prajwal1121/Portable-Synth/Version 2 (Latest)/Software/Groovebox_Platformio/include/Mixer.h

#ifndef MIXER_H
#define MIXER_H

#include <Arduino.h>

/*
 * Output Stuff
 */
extern float outputVolume[2];

class Mixer {
  private:
    void init();
  public:
    Mixer()
    {
      init();
    }
    void menuCheck();
    void staticMenu();
};

#endif
