prajwal1121/Portable-Synth/Version 1/Code/Sequencer+Recording/1_SequenceAndRecord/9_Metronome.ino

long metronomeTimer = millis();

void metronomePlayer(){
  if (metronomeEnable == 2){
    if (millis()-metronomeTimer > ms_per_beat){
      metronome.play(AudioSampleMetronome);
      if (armLocation){
        armLocation = 0;
      }
      else{
        armLocation = 1;
      }
      metronomeTimer = millis();
    }
  }
}

void tapMetronome(){
  metronome.play(AudioSampleMetronome);
  tapTempo.update();
  bpm = tapTempo.getBPM();
}
