prajwal1121/Portable-Synth/Version 1/Code/Sequencer+Recording/1_SequenceAndRecord/AudioSampleMetronome.cpp

// Audio data converted from WAV file by wav2sketch

#include "AudioSampleMetronome.h"

// Converted from metronome.wav, using 44100 Hz, u-law encoding
const unsigned int AudioSampleMetronome[6657] = {
0x01006797,0x98800080,0x90BC182D,0x2442321B,0x94B9C3C2,0x45403931,0xC5C1B038,0x1BB8C2CC,
0x595E594E,0xE8E2CF3D,0xB4DEE4E8,0x74726859,0xC5566D73,0xEAEAE8E2,0xE0E5E9EA,0xDAC9BED1,
0x40D3E3E1,0x7E7B7361,0x6773797E,0xE3D9C151,0xF2F1EBE8,0xF8F4F1F0,0xE1F1F9FA,0x76726391,
0x787C7C79,0x75737374,0xA65A6F75,0xFEF4E6D4,0xFFFFFFFF,0xE9F4F9FC,0x675C3BD3,0x7F7F7971,
0x7C7F7F7F,0x46657278,0xF8F2E7D2,0xFFFFFFFD,0xF9FEFFFF,0x7060CCEF,0x7C7B7975,0x7F7F7F7F,
0x70797E7F,0xF8F0D558,0xFFFFFFFF,0xF6FBFEFF,0xCBE5EEF2,0x7D766B53,0x7F7F7F7F,0x6C747B7F,
0xE5D04560,0xFFFAF6F1,0xFFFFFFFF,0xD6ECF6FC,0x7672664B,0x7E7E7C79,0x7A7D7E7E,0xC15D6F76,
0xFDF9F2E6,0xFFFFFFFF,0xF0F6FAFD,0x6A56C5E4,0x7F7D7973,0x7D7F7F7F,0x5E6D757A,0xF7F0E1A5,
0xFFFFFFFD,0xF7FCFEFF,0x4FCCE4F0,0x7D787266,0x7E7F7F7F,0x6A747A7C,0xEBDDAC58,0xFFFDF9F4,
0xFBFDFEFF,0xC5E4F1F7,0x76726753,0x7D7D7C7A,0x72767A7C,0xD73B606B,0xFBF7F3EA,0xFAFDFDFD,
0xE0EBF3F7,0x6C6147C7,0x7B797672,0x75787B7C,0xB3536570,0xF4F0E7DA,0xF9F9F9F7,0xEAF1F5F7,
0x624CC2DF,0x7775726C,0x74767778,0x52626B71,0xEDE4D6A2,0xF6F6F4F2,0xEDF2F4F6,0x4BB2D7E5,
0x726E675E,0x73747474,0x5E676E72,0xE2D3A94B,0xF3F2EFE9,0xEEF1F2F3,0xA9D3E1E8,0x6A655C4B,
0x7171706F,0x63696E70,0xD6BF4057,0xEEEBE7E1,0xEBEEEFEF,0xCFDBE3E8,0x635A49A2,0x6E6D6B67,
0x62666A6D,0xC032505A,0xE6E3DDD3,0xE9EAEAE9,0xD1DCE3E7,0x595036B9,0x66656360,0x61646666,
0x0246545C,0xE1DCD4C5,0xE3E4E4E3,0xD3D9DFE1,0x4B34B0C8,0x62605C55,0x5F616263,0x24435159,
0xD6D0C5B3,0xE0E0DFDB,0xD3D9DDE0,0x452BB5C8,0x5E5C5851,0x55595B5D,0x273E4850,0xCCC5BDA7,
0xD8D7D4D1,0xC9D1D5D8,0x413394BC,0x4D4B4946,0x4D50504E,0x3441464A,0xC3BDB010,0xCCCBC9C6,
0xBABFC4C9,0x3011A2B3,0x44403B38,0x3A404344,0x9E122E36,0xB8B3ABA4,0xBEC0C1BE,0x21A4B7BF,
0x41403C35,0x3032373E,0x182A2C2B,0xB1A19189,0xC6C8C5BF,0x9CB4C0C4,0x403E3623,0x41404040,
0x41434442,0xAC20343C,0xCCCAC7C1,0xC3C8CACC,0xAFB5B8BD,0x403315A3,0x52524F48,0x3B444D51,
0xB1A30D30,0xC7C2BDB8,0xD1D1CFCB,0xB2C3CBD0,0x46423922,0x4B4C4B4A,0x48494949,0x0D374246,
0xCDC7C0B2,0xCCD1D2D1,0xBAC0C2C6,0x302499B2,0x504A4338,0x494D5151,0x03313F45,0xC0BAB8B0,
0xC9C8C6C4,0xC2C6C8C9,0x169AAFB9,0x4540362A,0x47474747,0x36404446,0xB9AC0D2B,0xC3C1C0BF,
0xC5C6C6C5,0xA6B9C2C5,0x4540351F,0x484A4948,0x29323D44,0xA3012026,0xC4C0BBB2,0xC8C9C8C6,
0x1C9BB5C2,0x3E3A332A,0x3633373C,0x4041403D,0x182D353B,0xC4C2B8A4,0xC1C3C5C5,0x99A6B2BC,
0x28201505,0x3D3C3A33,0x4141403E,0x9120303A,0xC0BBB4A8,0xC2C3C3C1,0xA2AEB6BD,0x35281292,
0x4644423E,0x2F3A4246,0xBBB2A213,0xBABEC0C0,0xA0A7B1B6,0xAAA8A19B,0x372E159E,0x393D3C3A,
0xA3892332,0x8FA1A9A9,0x94870C0F,0xB2B1ACA2,0x27179BAC,0x282D2D2B,0xA095011D,0x9198A0A1,
0xA6A2978F,0xADAFACA9,0x2B208AA3,0x3534312F,0x23252C32,0x81182425,0xB3ADA397,0xBDBCBAB7,
0xA4AFB6BB,0x31271491,0x413E3935,0x343C4142,0x841D282F,0xB9B4B0A2,0xC3C2C1BE,0xB6BDC0C2,
0x2E2093AB,0x403E3B36,0x44424140,0x333C4345,0xBEB29C21,0xC4C6C6C4,0xBEC1C2C2,0xA4AFB4B9,
0x42392A00,0x4C4C4A46,0x333F4549,0xA89E8522,0xC4C1BAB3,0xCBCCCBC8,0xB2BCC3C8,0x3F372798,
0x48464342,0x484A4A49,0x26374044,0xC8C2B69C,0xCCCCCBCA,0xC0C4C7CA,0x298BAEB9,0x49444037,
0x4A4C4D4C,0x34404447,0xB9AD9422,0xCBCAC6C2,0xC6C9CBCC,0x9AB1BCC2,0x423C3423,0x4C4C4A46,
0x3F44484A,0xA8912033,0xC6C3BFB5,0xCCCCCAC8,0xB3BDC3C8,0x3E35239B,0x48474543,0x46474849,
0x28374044,0xC5C0B599,0xCACBCAC8,0xBEC3C7C9,0x2790ACB6,0x48444036,0x494B4C4B,0x2F3A4246,
0xB9B09F16,0xC9C8C5C1,0xC3C6C8C9,0x82A9B5BE,0x433C3327,0x49494745,0x38414547,0xB3A5072A,
0xC2C3C1BC,0xC6C5C3C2,0xB1B8C0C4,0x4239249F,0x44454645,0x38404243,0x99062430,0xBFB6ADA2,
0xC5C5C5C3,0xAEB9C0C3,0x29231695,0x43413B32,0x42444444,0x23323A40,0xB8B3A98A,0xC3C4C2BE,
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
};
