prajwal1121/Portable-Synth/Version 1/Code/Sequencer+Recording/1_SequenceAndRecord/Ocarina_samples.cpp

#include "Ocarina_samples.h"
const AudioSynthWavetable::sample_data Ocarina_samples[3] = {
	{
		(int16_t*)sample_0_Ocarina_OcarinaF4,	//16-bit PCM encoded audio sample
		true,	//Whether or not to loop this sample
		12,	//Number of bits needed to hold length
		(1048576*1.0227829387472833*(44100.0 / AUDIO_SAMPLE_RATE_EXACT)) / 1318.5102276514797 + 0.5,	//((0x80000000 >> (index_bits - 1)) * cents_offset * sampling_rate / AUDIO_SAME_RATE_EXACT) / sample_freq + 0.5
		((uint32_t)2847-1) << (32 - 12),	//(sample_length-1) << (32 - sample_length_bits)
		((uint32_t)2839-1) << (32 - 12),	//(loop_end-1) << (32 - sample_length_bits) == LOOP_PHASE_END
		(((uint32_t)2839-1) << (32 - 12)) - (((uint32_t)1438-1) << (32 - 12)),	//LOOP_PHASE_END - (loop_start-1) << (32 - sample_length_bits) == LOOP_PHASE_END - LOOP_PHASE_START == LOOP_PHASE_LENGTH
		uint16_t(UINT16_MAX * WAVETABLE_DECIBEL_SHIFT(-170/100.0)), //INITIAL_ATTENUATION_SCALAR
		uint32_t(0*AudioSynthWavetable::SAMPLES_PER_MSEC/8.0+0.5),	//DELAY_COUNT
		uint32_t(7*AudioSynthWavetable::SAMPLES_PER_MSEC/8.0+0.5),	//ATTACK_COUNT
		uint32_t(0*AudioSynthWavetable::SAMPLES_PER_MSEC/8.0+0.5),	//HOLD_COUNT
		uint32_t(1730*AudioSynthWavetable::SAMPLES_PER_MSEC/8.0+0.5),	//DECAY_COUNT
		uint32_t(321*AudioSynthWavetable::SAMPLES_PER_MSEC/8.0+0.5),	//RELEASE_COUNT
		int32_t(0*AudioSynthWavetable::UNITY_GAIN),	//SUSTAIN_MULT
		uint32_t(9 * AudioSynthWavetable::SAMPLES_PER_MSEC / (2 * AudioSynthWavetable::LFO_PERIOD)), 	// VIBRATO_DELAY
		uint32_t(4288/1000.0 * AudioSynthWavetable::LFO_PERIOD * (UINT32_MAX / AUDIO_SAMPLE_RATE_EXACT)), // VIBRATO_INCREMENT
		(WAVETABLE_CENTS_SHIFT(-0/1000.0) - 1.0)*4, // VIBRATO_PITCH_COEFFICIENT_INITIAL
		(1.0 - WAVETABLE_CENTS_SHIFT(0/1000.0))*4, // VIBRATO_COEFFICIENT_SECONDARY
		uint32_t(14 * AudioSynthWavetable::SAMPLES_PER_MSEC / (2 * AudioSynthWavetable::LFO_PERIOD)), // MODULATION_DELAY
		uint32_t(4288/1000.0 * AudioSynthWavetable::LFO_PERIOD * (UINT32_MAX / AUDIO_SAMPLE_RATE_EXACT)), // MODULATION_INCREMENT
		(WAVETABLE_CENTS_SHIFT(-0/1000.0) - 1.0)*4, // MODULATION_PITCH_COEFFICIENT_INITIAL
		(1.0 - WAVETABLE_CENTS_SHIFT(0/1000.0))*4, // MODULATION_PITCH_COEFFICIENT_SECOND
		int32_t(UINT16_MAX * (WAVETABLE_DECIBEL_SHIFT(-0.1) - 1.0)) *4, // MODULATION_AMPLITUDE_INITIAL_GAIN
		int32_t(UINT16_MAX * (1.0 - WAVETABLE_DECIBEL_SHIFT(0.1))) *4, // MODULATION_AMPLITUDE_FINAL_GAIN
	},
	{
		(int16_t*)sample_1_Ocarina_OcarinaF4,	//16-bit PCM encoded audio sample
		true,	//Whether or not to loop this sample
		12,	//Number of bits needed to hold length
		(1048576*1.023373891996775*(44100.0 / AUDIO_SAMPLE_RATE_EXACT)) / 1318.5102276514797 + 0.5,	//((0x80000000 >> (index_bits - 1)) * cents_offset * sampling_rate / AUDIO_SAME_RATE_EXACT) / sample_freq + 0.5
		((uint32_t)2847-1) << (32 - 12),	//(sample_length-1) << (32 - sample_length_bits)
		((uint32_t)2839-1) << (32 - 12),	//(loop_end-1) << (32 - sample_length_bits) == LOOP_PHASE_END
		(((uint32_t)2839-1) << (32 - 12)) - (((uint32_t)1438-1) << (32 - 12)),	//LOOP_PHASE_END - (loop_start-1) << (32 - sample_length_bits) == LOOP_PHASE_END - LOOP_PHASE_START == LOOP_PHASE_LENGTH
		uint16_t(UINT16_MAX * WAVETABLE_DECIBEL_SHIFT(-100/100.0)), //INITIAL_ATTENUATION_SCALAR
		uint32_t(0*AudioSynthWavetable::SAMPLES_PER_MSEC/8.0+0.5),	//DELAY_COUNT
		uint32_t(7*AudioSynthWavetable::SAMPLES_PER_MSEC/8.0+0.5),	//ATTACK_COUNT
		uint32_t(0*AudioSynthWavetable::SAMPLES_PER_MSEC/8.0+0.5),	//HOLD_COUNT
		uint32_t(1730*AudioSynthWavetable::SAMPLES_PER_MSEC/8.0+0.5),	//DECAY_COUNT
		uint32_t(321*AudioSynthWavetable::SAMPLES_PER_MSEC/8.0+0.5),	//RELEASE_COUNT
		int32_t(0*AudioSynthWavetable::UNITY_GAIN),	//SUSTAIN_MULT
		uint32_t(9 * AudioSynthWavetable::SAMPLES_PER_MSEC / (2 * AudioSynthWavetable::LFO_PERIOD)), 	// VIBRATO_DELAY
		uint32_t(4288/1000.0 * AudioSynthWavetable::LFO_PERIOD * (UINT32_MAX / AUDIO_SAMPLE_RATE_EXACT)), // VIBRATO_INCREMENT
		(WAVETABLE_CENTS_SHIFT(-0/1000.0) - 1.0)*4, // VIBRATO_PITCH_COEFFICIENT_INITIAL
		(1.0 - WAVETABLE_CENTS_SHIFT(0/1000.0))*4, // VIBRATO_COEFFICIENT_SECONDARY
		uint32_t(14 * AudioSynthWavetable::SAMPLES_PER_MSEC / (2 * AudioSynthWavetable::LFO_PERIOD)), // MODULATION_DELAY
		uint32_t(4288/1000.0 * AudioSynthWavetable::LFO_PERIOD * (UINT32_MAX / AUDIO_SAMPLE_RATE_EXACT)), // MODULATION_INCREMENT
		(WAVETABLE_CENTS_SHIFT(-0/1000.0) - 1.0)*4, // MODULATION_PITCH_COEFFICIENT_INITIAL
		(1.0 - WAVETABLE_CENTS_SHIFT(0/1000.0))*4, // MODULATION_PITCH_COEFFICIENT_SECOND
		int32_t(UINT16_MAX * (WAVETABLE_DECIBEL_SHIFT(-0.1) - 1.0)) *4, // MODULATION_AMPLITUDE_INITIAL_GAIN
		int32_t(UINT16_MAX * (1.0 - WAVETABLE_DECIBEL_SHIFT(0.1))) *4, // MODULATION_AMPLITUDE_FINAL_GAIN
	},
	{
		(int16_t*)sample_2_Ocarina_OcarinaF6,	//16-bit PCM encoded audio sample
		true,	//Whether or not to loop this sample
		9,	//Number of bits needed to hold length
		(8388608*1.0*(44100.0 / AUDIO_SAMPLE_RATE_EXACT)) / 4434.922095629953 + 0.5,	//((0x80000000 >> (index_bits - 1)) * cents_offset * sampling_rate / AUDIO_SAME_RATE_EXACT) / sample_freq + 0.5
		((uint32_t)349-1) << (32 - 9),	//(sample_length-1) << (32 - sample_length_bits)
		((uint32_t)341-1) << (32 - 9),	//(loop_end-1) << (32 - sample_length_bits) == LOOP_PHASE_END
		(((uint32_t)341-1) << (32 - 9)) - (((uint32_t)331-1) << (32 - 9)),	//LOOP_PHASE_END - (loop_start-1) << (32 - sample_length_bits) == LOOP_PHASE_END - LOOP_PHASE_START == LOOP_PHASE_LENGTH
		uint16_t(UINT16_MAX * WAVETABLE_DECIBEL_SHIFT(-170/100.0)), //INITIAL_ATTENUATION_SCALAR
		uint32_t(0*AudioSynthWavetable::SAMPLES_PER_MSEC/8.0+0.5),	//DELAY_COUNT
		uint32_t(10*AudioSynthWavetable::SAMPLES_PER_MSEC/8.0+0.5),	//ATTACK_COUNT
		uint32_t(0*AudioSynthWavetable::SAMPLES_PER_MSEC/8.0+0.5),	//HOLD_COUNT
		uint32_t(1730*AudioSynthWavetable::SAMPLES_PER_MSEC/8.0+0.5),	//DECAY_COUNT
		uint32_t(321*AudioSynthWavetable::SAMPLES_PER_MSEC/8.0+0.5),	//RELEASE_COUNT
		int32_t(0*AudioSynthWavetable::UNITY_GAIN),	//SUSTAIN_MULT
		uint32_t(9 * AudioSynthWavetable::SAMPLES_PER_MSEC / (2 * AudioSynthWavetable::LFO_PERIOD)), 	// VIBRATO_DELAY
		uint32_t(4288/1000.0 * AudioSynthWavetable::LFO_PERIOD * (UINT32_MAX / AUDIO_SAMPLE_RATE_EXACT)), // VIBRATO_INCREMENT
		(WAVETABLE_CENTS_SHIFT(-0/1000.0) - 1.0)*4, // VIBRATO_PITCH_COEFFICIENT_INITIAL
		(1.0 - WAVETABLE_CENTS_SHIFT(0/1000.0))*4, // VIBRATO_COEFFICIENT_SECONDARY
		uint32_t(14 * AudioSynthWavetable::SAMPLES_PER_MSEC / (2 * AudioSynthWavetable::LFO_PERIOD)), // MODULATION_DELAY
		uint32_t(4288/1000.0 * AudioSynthWavetable::LFO_PERIOD * (UINT32_MAX / AUDIO_SAMPLE_RATE_EXACT)), // MODULATION_INCREMENT
		(WAVETABLE_CENTS_SHIFT(-0/1000.0) - 1.0)*4, // MODULATION_PITCH_COEFFICIENT_INITIAL
		(1.0 - WAVETABLE_CENTS_SHIFT(0/1000.0))*4, // MODULATION_PITCH_COEFFICIENT_SECOND
		int32_t(UINT16_MAX * (WAVETABLE_DECIBEL_SHIFT(-0.1) - 1.0)) *4, // MODULATION_AMPLITUDE_INITIAL_GAIN
		int32_t(UINT16_MAX * (1.0 - WAVETABLE_DECIBEL_SHIFT(0.1))) *4, // MODULATION_AMPLITUDE_FINAL_GAIN
	},
};

PROGMEM const uint32_t sample_0_Ocarina_OcarinaF4[1536] = {
0x016601b0,0x01550152,0x0180014c,0x019a01b7,0x025c01d8,0x030a02b4,0x026c02e9,0x01900220,
0x012300de,0x00db0106,0x01a7016e,0x0089011f,0x005a0012,0x005a0051,0x01ac00e3,0x01b60199,
0x00cd0155,0x016d0152,0x01e901c8,0x012f01aa,0x014a0190,0x01b00166,0x025e028b,0x02920268,
0x018b021a,0x012d00f6,0x01ac01b7,0x028e01f1,0x029502f2,0x01d201fb,0x01590215,0x00fa011a,
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
0x00000000,0x00000000,0x00000000,0x00000000,0x00000000,0x00000000,0x00000000,0x00000000,
0x00000000,0x00000000,0x00000000,0x00000000,0x00000000,0x00000000,0x00000000,0x00000000,
0x00000000,0x00000000,0x00000000,0x00000000,
};
