prajwal1121/Portable-Synth/Version 1/Code/Sequencer+Recording/1_SequenceAndRecord/Pizzicato_samples.cpp

#include "Pizzicato_samples.h"
const AudioSynthWavetable::sample_data Pizzicato_samples[4] = {
	{
		(int16_t*)sample_0_Pizzicato_PizzViolinE3,	//16-bit PCM encoded audio sample
		true,	//Whether or not to loop this sample
		13,	//Number of bits needed to hold length
		(524288*1.0*(44100.0 / AUDIO_SAMPLE_RATE_EXACT)) / 622.2539674441618 + 0.5,	//((0x80000000 >> (index_bits - 1)) * cents_offset * sampling_rate / AUDIO_SAME_RATE_EXACT) / sample_freq + 0.5
		((uint32_t)5687-1) << (32 - 13),	//(sample_length-1) << (32 - sample_length_bits)
		((uint32_t)5679-1) << (32 - 13),	//(loop_end-1) << (32 - sample_length_bits) == LOOP_PHASE_END
		(((uint32_t)5679-1) << (32 - 13)) - (((uint32_t)5608-1) << (32 - 13)),	//LOOP_PHASE_END - (loop_start-1) << (32 - sample_length_bits) == LOOP_PHASE_END - LOOP_PHASE_START == LOOP_PHASE_LENGTH
		uint16_t(UINT16_MAX * WAVETABLE_DECIBEL_SHIFT(-550/100.0)), //INITIAL_ATTENUATION_SCALAR
		uint32_t(0*AudioSynthWavetable::SAMPLES_PER_MSEC/8.0+0.5),	//DELAY_COUNT
		uint32_t(0*AudioSynthWavetable::SAMPLES_PER_MSEC/8.0+0.5),	//ATTACK_COUNT
		uint32_t(0*AudioSynthWavetable::SAMPLES_PER_MSEC/8.0+0.5),	//HOLD_COUNT
		uint32_t(4110*AudioSynthWavetable::SAMPLES_PER_MSEC/8.0+0.5),	//DECAY_COUNT
		uint32_t(2940*AudioSynthWavetable::SAMPLES_PER_MSEC/8.0+0.5),	//RELEASE_COUNT
		int32_t(1*AudioSynthWavetable::UNITY_GAIN),	//SUSTAIN_MULT
		uint32_t(9 * AudioSynthWavetable::SAMPLES_PER_MSEC / (2 * AudioSynthWavetable::LFO_PERIOD)), 	// VIBRATO_DELAY
		uint32_t(5129/1000.0 * AudioSynthWavetable::LFO_PERIOD * (UINT32_MAX / AUDIO_SAMPLE_RATE_EXACT)), // VIBRATO_INCREMENT
		(WAVETABLE_CENTS_SHIFT(-0/1000.0) - 1.0)*4, // VIBRATO_PITCH_COEFFICIENT_INITIAL
		(1.0 - WAVETABLE_CENTS_SHIFT(0/1000.0))*4, // VIBRATO_COEFFICIENT_SECONDARY
		uint32_t(9 * AudioSynthWavetable::SAMPLES_PER_MSEC / (2 * AudioSynthWavetable::LFO_PERIOD)), // MODULATION_DELAY
		uint32_t(5129/1000.0 * AudioSynthWavetable::LFO_PERIOD * (UINT32_MAX / AUDIO_SAMPLE_RATE_EXACT)), // MODULATION_INCREMENT
		(WAVETABLE_CENTS_SHIFT(-0/1000.0) - 1.0)*4, // MODULATION_PITCH_COEFFICIENT_INITIAL
		(1.0 - WAVETABLE_CENTS_SHIFT(0/1000.0))*4, // MODULATION_PITCH_COEFFICIENT_SECOND
		int32_t(UINT16_MAX * (WAVETABLE_DECIBEL_SHIFT(-0.1) - 1.0)) *4, // MODULATION_AMPLITUDE_INITIAL_GAIN
		int32_t(UINT16_MAX * (1.0 - WAVETABLE_DECIBEL_SHIFT(0.1))) *4, // MODULATION_AMPLITUDE_FINAL_GAIN
	},
	{
		(int16_t*)sample_1_Pizzicato_PizzViolinC4,	//16-bit PCM encoded audio sample
		true,	//Whether or not to loop this sample
		13,	//Number of bits needed to hold length
		(524288*1.0*(44100.0 / AUDIO_SAMPLE_RATE_EXACT)) / 1046.5022612023945 + 0.5,	//((0x80000000 >> (index_bits - 1)) * cents_offset * sampling_rate / AUDIO_SAME_RATE_EXACT) / sample_freq + 0.5
		((uint32_t)4607-1) << (32 - 13),	//(sample_length-1) << (32 - sample_length_bits)
		((uint32_t)4599-1) << (32 - 13),	//(loop_end-1) << (32 - sample_length_bits) == LOOP_PHASE_END
		(((uint32_t)4599-1) << (32 - 13)) - (((uint32_t)4557-1) << (32 - 13)),	//LOOP_PHASE_END - (loop_start-1) << (32 - sample_length_bits) == LOOP_PHASE_END - LOOP_PHASE_START == LOOP_PHASE_LENGTH
		uint16_t(UINT16_MAX * WAVETABLE_DECIBEL_SHIFT(-550/100.0)), //INITIAL_ATTENUATION_SCALAR
		uint32_t(0*AudioSynthWavetable::SAMPLES_PER_MSEC/8.0+0.5),	//DELAY_COUNT
		uint32_t(0*AudioSynthWavetable::SAMPLES_PER_MSEC/8.0+0.5),	//ATTACK_COUNT
		uint32_t(0*AudioSynthWavetable::SAMPLES_PER_MSEC/8.0+0.5),	//HOLD_COUNT
		uint32_t(3929*AudioSynthWavetable::SAMPLES_PER_MSEC/8.0+0.5),	//DECAY_COUNT
		uint32_t(2849*AudioSynthWavetable::SAMPLES_PER_MSEC/8.0+0.5),	//RELEASE_COUNT
		int32_t(1*AudioSynthWavetable::UNITY_GAIN),	//SUSTAIN_MULT
		uint32_t(9 * AudioSynthWavetable::SAMPLES_PER_MSEC / (2 * AudioSynthWavetable::LFO_PERIOD)), 	// VIBRATO_DELAY
		uint32_t(5129/1000.0 * AudioSynthWavetable::LFO_PERIOD * (UINT32_MAX / AUDIO_SAMPLE_RATE_EXACT)), // VIBRATO_INCREMENT
		(WAVETABLE_CENTS_SHIFT(-0/1000.0) - 1.0)*4, // VIBRATO_PITCH_COEFFICIENT_INITIAL
		(1.0 - WAVETABLE_CENTS_SHIFT(0/1000.0))*4, // VIBRATO_COEFFICIENT_SECONDARY
		uint32_t(9 * AudioSynthWavetable::SAMPLES_PER_MSEC / (2 * AudioSynthWavetable::LFO_PERIOD)), // MODULATION_DELAY
		uint32_t(5129/1000.0 * AudioSynthWavetable::LFO_PERIOD * (UINT32_MAX / AUDIO_SAMPLE_RATE_EXACT)), // MODULATION_INCREMENT
		(WAVETABLE_CENTS_SHIFT(-0/1000.0) - 1.0)*4, // MODULATION_PITCH_COEFFICIENT_INITIAL
		(1.0 - WAVETABLE_CENTS_SHIFT(0/1000.0))*4, // MODULATION_PITCH_COEFFICIENT_SECOND
		int32_t(UINT16_MAX * (WAVETABLE_DECIBEL_SHIFT(-0.1) - 1.0)) *4, // MODULATION_AMPLITUDE_INITIAL_GAIN
		int32_t(UINT16_MAX * (1.0 - WAVETABLE_DECIBEL_SHIFT(0.1))) *4, // MODULATION_AMPLITUDE_FINAL_GAIN
	},
	{
		(int16_t*)sample_2_Pizzicato_PizzViolinE5,	//16-bit PCM encoded audio sample
		true,	//Whether or not to loop this sample
		11,	//Number of bits needed to hold length
		(2097152*1.0157180609309646*(44100.0 / AUDIO_SAMPLE_RATE_EXACT)) / 2793.825851464031 + 0.5,	//((0x80000000 >> (index_bits - 1)) * cents_offset * sampling_rate / AUDIO_SAME_RATE_EXACT) / sample_freq + 0.5
		((uint32_t)1355-1) << (32 - 11),	//(sample_length-1) << (32 - sample_length_bits)
		((uint32_t)1347-1) << (32 - 11),	//(loop_end-1) << (32 - sample_length_bits) == LOOP_PHASE_END
		(((uint32_t)1347-1) << (32 - 11)) - (((uint32_t)1331-1) << (32 - 11)),	//LOOP_PHASE_END - (loop_start-1) << (32 - sample_length_bits) == LOOP_PHASE_END - LOOP_PHASE_START == LOOP_PHASE_LENGTH
		uint16_t(UINT16_MAX * WAVETABLE_DECIBEL_SHIFT(-550/100.0)), //INITIAL_ATTENUATION_SCALAR
		uint32_t(0*AudioSynthWavetable::SAMPLES_PER_MSEC/8.0+0.5),	//DELAY_COUNT
		uint32_t(0*AudioSynthWavetable::SAMPLES_PER_MSEC/8.0+0.5),	//ATTACK_COUNT
		uint32_t(0*AudioSynthWavetable::SAMPLES_PER_MSEC/8.0+0.5),	//HOLD_COUNT
		uint32_t(2569*AudioSynthWavetable::SAMPLES_PER_MSEC/8.0+0.5),	//DECAY_COUNT
		uint32_t(1449*AudioSynthWavetable::SAMPLES_PER_MSEC/8.0+0.5),	//RELEASE_COUNT
		int32_t(1*AudioSynthWavetable::UNITY_GAIN),	//SUSTAIN_MULT
		uint32_t(9 * AudioSynthWavetable::SAMPLES_PER_MSEC / (2 * AudioSynthWavetable::LFO_PERIOD)), 	// VIBRATO_DELAY
		uint32_t(5129/1000.0 * AudioSynthWavetable::LFO_PERIOD * (UINT32_MAX / AUDIO_SAMPLE_RATE_EXACT)), // VIBRATO_INCREMENT
		(WAVETABLE_CENTS_SHIFT(-0/1000.0) - 1.0)*4, // VIBRATO_PITCH_COEFFICIENT_INITIAL
		(1.0 - WAVETABLE_CENTS_SHIFT(0/1000.0))*4, // VIBRATO_COEFFICIENT_SECONDARY
		uint32_t(9 * AudioSynthWavetable::SAMPLES_PER_MSEC / (2 * AudioSynthWavetable::LFO_PERIOD)), // MODULATION_DELAY
		uint32_t(5129/1000.0 * AudioSynthWavetable::LFO_PERIOD * (UINT32_MAX / AUDIO_SAMPLE_RATE_EXACT)), // MODULATION_INCREMENT
		(WAVETABLE_CENTS_SHIFT(-0/1000.0) - 1.0)*4, // MODULATION_PITCH_COEFFICIENT_INITIAL
		(1.0 - WAVETABLE_CENTS_SHIFT(0/1000.0))*4, // MODULATION_PITCH_COEFFICIENT_SECOND
		int32_t(UINT16_MAX * (WAVETABLE_DECIBEL_SHIFT(-0.1) - 1.0)) *4, // MODULATION_AMPLITUDE_INITIAL_GAIN
		int32_t(UINT16_MAX * (1.0 - WAVETABLE_DECIBEL_SHIFT(0.1))) *4, // MODULATION_AMPLITUDE_FINAL_GAIN
	},
	{
		(int16_t*)sample_3_Pizzicato_PizzViolinE5,	//16-bit PCM encoded audio sample
		true,	//Whether or not to loop this sample
		11,	//Number of bits needed to hold length
		(2097152*1.0157180609309646*(44100.0 / AUDIO_SAMPLE_RATE_EXACT)) / 2793.825851464031 + 0.5,	//((0x80000000 >> (index_bits - 1)) * cents_offset * sampling_rate / AUDIO_SAME_RATE_EXACT) / sample_freq + 0.5
		((uint32_t)1355-1) << (32 - 11),	//(sample_length-1) << (32 - sample_length_bits)
		((uint32_t)1347-1) << (32 - 11),	//(loop_end-1) << (32 - sample_length_bits) == LOOP_PHASE_END
		(((uint32_t)1347-1) << (32 - 11)) - (((uint32_t)1331-1) << (32 - 11)),	//LOOP_PHASE_END - (loop_start-1) << (32 - sample_length_bits) == LOOP_PHASE_END - LOOP_PHASE_START == LOOP_PHASE_LENGTH
		uint16_t(UINT16_MAX * WAVETABLE_DECIBEL_SHIFT(-550/100.0)), //INITIAL_ATTENUATION_SCALAR
		uint32_t(0*AudioSynthWavetable::SAMPLES_PER_MSEC/8.0+0.5),	//DELAY_COUNT
		uint32_t(0*AudioSynthWavetable::SAMPLES_PER_MSEC/8.0+0.5),	//ATTACK_COUNT
		uint32_t(0*AudioSynthWavetable::SAMPLES_PER_MSEC/8.0+0.5),	//HOLD_COUNT
		uint32_t(2329*AudioSynthWavetable::SAMPLES_PER_MSEC/8.0+0.5),	//DECAY_COUNT
		uint32_t(1309*AudioSynthWavetable::SAMPLES_PER_MSEC/8.0+0.5),	//RELEASE_COUNT
		int32_t(1*AudioSynthWavetable::UNITY_GAIN),	//SUSTAIN_MULT
		uint32_t(9 * AudioSynthWavetable::SAMPLES_PER_MSEC / (2 * AudioSynthWavetable::LFO_PERIOD)), 	// VIBRATO_DELAY
		uint32_t(5129/1000.0 * AudioSynthWavetable::LFO_PERIOD * (UINT32_MAX / AUDIO_SAMPLE_RATE_EXACT)), // VIBRATO_INCREMENT
		(WAVETABLE_CENTS_SHIFT(-0/1000.0) - 1.0)*4, // VIBRATO_PITCH_COEFFICIENT_INITIAL
		(1.0 - WAVETABLE_CENTS_SHIFT(0/1000.0))*4, // VIBRATO_COEFFICIENT_SECONDARY
		uint32_t(9 * AudioSynthWavetable::SAMPLES_PER_MSEC / (2 * AudioSynthWavetable::LFO_PERIOD)), // MODULATION_DELAY
		uint32_t(5129/1000.0 * AudioSynthWavetable::LFO_PERIOD * (UINT32_MAX / AUDIO_SAMPLE_RATE_EXACT)), // MODULATION_INCREMENT
		(WAVETABLE_CENTS_SHIFT(-0/1000.0) - 1.0)*4, // MODULATION_PITCH_COEFFICIENT_INITIAL
		(1.0 - WAVETABLE_CENTS_SHIFT(0/1000.0))*4, // MODULATION_PITCH_COEFFICIENT_SECOND
		int32_t(UINT16_MAX * (WAVETABLE_DECIBEL_SHIFT(-0.1) - 1.0)) *4, // MODULATION_AMPLITUDE_INITIAL_GAIN
		int32_t(UINT16_MAX * (1.0 - WAVETABLE_DECIBEL_SHIFT(0.1))) *4, // MODULATION_AMPLITUDE_FINAL_GAIN
	},
};

PROGMEM const uint32_t sample_0_Pizzicato_PizzViolinE3[2944] = {
0xffeeffbc,0x03230104,0x062004f3,0x0d4f07cb,0x1c351736,0x16ae18bd,0x1cad1a19,0x1ed81ede,
0x1a1b1b79,0x1ea61c1e,0x11081a2f,0x074a0a00,0x034305c7,0x012e02b7,0xf781fc58,0xf5d7f770,
0xeee8f0ff,0xf371f15c,0xef28f0cc,0xede5f0bd,0xe732e7dd,0xebbbea4d,0xed82eb55,0xf290f040,
0xee91f29a,0xf701f0c4,0xf7a6f4b1,0xfdd4fe96,0xf0b0f71e,0xfbbef36a,0x092e02ae,0x0ced0f60,
0x0d2608b1,0x0458132a,0x0e8806b3,0x1a481173,0x20e522d4,0x27291a4f,0x08911e87,0x09ee04e7,
0x1da30f8e,0x2bd62b41,0x0c131ff1,0xe059ed1c,0xf1fbe235,0xf8c8f96b,0xd543ee0c,0xd6ead00b,
0xd392d175,0xee0ae952,0xe826e46f,0xdcd5e6c6,0xe04ee179,0xe420e191,0x06edf0d0,0x0cf50986,
0xf7dd0c93,0x080ff61d,0x05440d94,0x0cc702b9,0x1e411675,0x2129212d,0x1e9e22df,0xfecc0f69,
0x061afdcd,0x219c14d3,0x1e6a247a,0x07fa1447,0xfc4ffe52,0x122d04fd,0x2f712104,0x27a43038,
0x3545292a,0x2fc73706,0x1b0626f1,0x116c118a,0x190a1217,0x02cf1843,0xde2aed6f,0xd609d122,
0xe451e85f,0xa074c17b,0x9ad39b63,0xb5149f6a,0xb084ba89,0xb02dae2b,0xb9fab61d,0xab0eb1f3,
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
0xecf1f10a,0x1787f8db,0x1d112e11,0x1bea2928,0xd656f0c7,0xe3b3c384,0x03e8f3b7,0x146615cd,
0x01230976,0x28150a4b,0x12462dce,0xfc8413a9,0xc093dd15,0xda66b3a6,0x0630f258,0x1149124b,
0x00270dbe,0x358f0ed6,0x1c22324c,0x02d81c21,0xc564ed27,0xe4abc1c7,0x13c5fd95,0x101b152a,
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
};
