prajwal1121/Portable-Synth/Version 1/Code/Sequencer+Recording/1_SequenceAndRecord/distortiongt_samples.cpp

#include "distortiongt_samples.h"
const AudioSynthWavetable::sample_data distortiongt_samples[4] = {
	{
		(int16_t*)sample_0_distortiongt_distgtra2, // sample
		true, // LOOP
		11, // LENGTH_BITS
		(1 << (32 - 11)) * WAVETABLE_CENTS_SHIFT(-45) * 44100.0 / WAVETABLE_NOTE_TO_FREQUENCY(72) / AUDIO_SAMPLE_RATE_EXACT + 0.5, // PER_HERTZ_PHASE_INCREMENT
		((uint32_t)1831 - 1) << (32 - 11), // MAX_PHASE
		((uint32_t)1827 - 1) << (32 - 11), // LOOP_PHASE_END
		(((uint32_t)1827 - 1) << (32 - 11)) - (((uint32_t)1745 - 1) << (32 - 11)), // LOOP_PHASE_LENGTH
		uint16_t(UINT16_MAX * WAVETABLE_DECIBEL_SHIFT(-7.5)), // INITIAL_ATTENUATION_SCALAR
		uint32_t(0.00 * AudioSynthWavetable::SAMPLES_PER_MSEC / AudioSynthWavetable::ENVELOPE_PERIOD + 0.5), // DELAY_COUNT
		uint32_t(6.20 * AudioSynthWavetable::SAMPLES_PER_MSEC / AudioSynthWavetable::ENVELOPE_PERIOD + 0.5), // ATTACK_COUNT
		uint32_t(20.01 * AudioSynthWavetable::SAMPLES_PER_MSEC / AudioSynthWavetable::ENVELOPE_PERIOD + 0.5), // HOLD_COUNT
		uint32_t(19596.17 * AudioSynthWavetable::SAMPLES_PER_MSEC / AudioSynthWavetable::ENVELOPE_PERIOD + 0.5), // DECAY_COUNT
		uint32_t(100.02 * AudioSynthWavetable::SAMPLES_PER_MSEC / AudioSynthWavetable::ENVELOPE_PERIOD + 0.5), // RELEASE_COUNT
		int32_t((1.0 - WAVETABLE_DECIBEL_SHIFT(-91.6)) * AudioSynthWavetable::UNITY_GAIN), // SUSTAIN_MULT
		uint32_t(0.00 * AudioSynthWavetable::SAMPLES_PER_MSEC / (2 * AudioSynthWavetable::LFO_PERIOD)), // VIBRATO_DELAY
		uint32_t(0.1 * AudioSynthWavetable::LFO_PERIOD * (UINT32_MAX / AUDIO_SAMPLE_RATE_EXACT)), // VIBRATO_INCREMENT
		(WAVETABLE_CENTS_SHIFT(0) - 1.0) * 4, // VIBRATO_PITCH_COEFFICIENT_INITIAL
		(1.0 - WAVETABLE_CENTS_SHIFT(0)) * 4, // VIBRATO_COEFFICIENT_SECONDARY
		uint32_t(0.00 * AudioSynthWavetable::SAMPLES_PER_MSEC / (2 * AudioSynthWavetable::LFO_PERIOD)), // MODULATION_DELAY
		uint32_t(5.4 * AudioSynthWavetable::LFO_PERIOD * (UINT32_MAX / AUDIO_SAMPLE_RATE_EXACT)), // MODULATION_INCREMENT
		(WAVETABLE_CENTS_SHIFT(0) - 1.0) * 4, // MODULATION_PITCH_COEFFICIENT_INITIAL
		(1.0 - WAVETABLE_CENTS_SHIFT(0)) * 4, // MODULATION_PITCH_COEFFICIENT_SECOND
		int32_t(UINT16_MAX * (WAVETABLE_DECIBEL_SHIFT(0) - 1.0)) * 4, // MODULATION_AMPLITUDE_INITIAL_GAIN
		int32_t(UINT16_MAX * (1.0 - WAVETABLE_DECIBEL_SHIFT(0))) * 4, // MODULATION_AMPLITUDE_FINAL_GAIN
	},
	{
		(int16_t*)sample_1_distortiongt_distgtre3, // sample
		true, // LOOP
		11, // LENGTH_BITS
		(1 << (32 - 11)) * WAVETABLE_CENTS_SHIFT(-35) * 44100.0 / WAVETABLE_NOTE_TO_FREQUENCY(79) / AUDIO_SAMPLE_RATE_EXACT + 0.5, // PER_HERTZ_PHASE_INCREMENT
		((uint32_t)1431 - 1) << (32 - 11), // MAX_PHASE
		((uint32_t)1427 - 1) << (32 - 11), // LOOP_PHASE_END
		(((uint32_t)1427 - 1) << (32 - 11)) - (((uint32_t)1372 - 1) << (32 - 11)), // LOOP_PHASE_LENGTH
		uint16_t(UINT16_MAX * WAVETABLE_DECIBEL_SHIFT(-7.5)), // INITIAL_ATTENUATION_SCALAR
		uint32_t(0.00 * AudioSynthWavetable::SAMPLES_PER_MSEC / AudioSynthWavetable::ENVELOPE_PERIOD + 0.5), // DELAY_COUNT
		uint32_t(6.20 * AudioSynthWavetable::SAMPLES_PER_MSEC / AudioSynthWavetable::ENVELOPE_PERIOD + 0.5), // ATTACK_COUNT
		uint32_t(20.01 * AudioSynthWavetable::SAMPLES_PER_MSEC / AudioSynthWavetable::ENVELOPE_PERIOD + 0.5), // HOLD_COUNT
		uint32_t(19596.17 * AudioSynthWavetable::SAMPLES_PER_MSEC / AudioSynthWavetable::ENVELOPE_PERIOD + 0.5), // DECAY_COUNT
		uint32_t(100.02 * AudioSynthWavetable::SAMPLES_PER_MSEC / AudioSynthWavetable::ENVELOPE_PERIOD + 0.5), // RELEASE_COUNT
		int32_t((1.0 - WAVETABLE_DECIBEL_SHIFT(-91.6)) * AudioSynthWavetable::UNITY_GAIN), // SUSTAIN_MULT
		uint32_t(0.00 * AudioSynthWavetable::SAMPLES_PER_MSEC / (2 * AudioSynthWavetable::LFO_PERIOD)), // VIBRATO_DELAY
		uint32_t(0.1 * AudioSynthWavetable::LFO_PERIOD * (UINT32_MAX / AUDIO_SAMPLE_RATE_EXACT)), // VIBRATO_INCREMENT
		(WAVETABLE_CENTS_SHIFT(0) - 1.0) * 4, // VIBRATO_PITCH_COEFFICIENT_INITIAL
		(1.0 - WAVETABLE_CENTS_SHIFT(0)) * 4, // VIBRATO_COEFFICIENT_SECONDARY
		uint32_t(0.00 * AudioSynthWavetable::SAMPLES_PER_MSEC / (2 * AudioSynthWavetable::LFO_PERIOD)), // MODULATION_DELAY
		uint32_t(5.4 * AudioSynthWavetable::LFO_PERIOD * (UINT32_MAX / AUDIO_SAMPLE_RATE_EXACT)), // MODULATION_INCREMENT
		(WAVETABLE_CENTS_SHIFT(0) - 1.0) * 4, // MODULATION_PITCH_COEFFICIENT_INITIAL
		(1.0 - WAVETABLE_CENTS_SHIFT(0)) * 4, // MODULATION_PITCH_COEFFICIENT_SECOND
		int32_t(UINT16_MAX * (WAVETABLE_DECIBEL_SHIFT(0) - 1.0)) * 4, // MODULATION_AMPLITUDE_INITIAL_GAIN
		int32_t(UINT16_MAX * (1.0 - WAVETABLE_DECIBEL_SHIFT(0))) * 4, // MODULATION_AMPLITUDE_FINAL_GAIN
	},
	{
		(int16_t*)sample_2_distortiongt_distgtra3, // sample
		true, // LOOP
		11, // LENGTH_BITS
		(1 << (32 - 11)) * WAVETABLE_CENTS_SHIFT(38) * 44100.0 / WAVETABLE_NOTE_TO_FREQUENCY(84) / AUDIO_SAMPLE_RATE_EXACT + 0.5, // PER_HERTZ_PHASE_INCREMENT
		((uint32_t)1242 - 1) << (32 - 11), // MAX_PHASE
		((uint32_t)1238 - 1) << (32 - 11), // LOOP_PHASE_END
		(((uint32_t)1238 - 1) << (32 - 11)) - (((uint32_t)1195 - 1) << (32 - 11)), // LOOP_PHASE_LENGTH
		uint16_t(UINT16_MAX * WAVETABLE_DECIBEL_SHIFT(-7.5)), // INITIAL_ATTENUATION_SCALAR
		uint32_t(0.00 * AudioSynthWavetable::SAMPLES_PER_MSEC / AudioSynthWavetable::ENVELOPE_PERIOD + 0.5), // DELAY_COUNT
		uint32_t(6.20 * AudioSynthWavetable::SAMPLES_PER_MSEC / AudioSynthWavetable::ENVELOPE_PERIOD + 0.5), // ATTACK_COUNT
		uint32_t(20.01 * AudioSynthWavetable::SAMPLES_PER_MSEC / AudioSynthWavetable::ENVELOPE_PERIOD + 0.5), // HOLD_COUNT
		uint32_t(19596.17 * AudioSynthWavetable::SAMPLES_PER_MSEC / AudioSynthWavetable::ENVELOPE_PERIOD + 0.5), // DECAY_COUNT
		uint32_t(100.02 * AudioSynthWavetable::SAMPLES_PER_MSEC / AudioSynthWavetable::ENVELOPE_PERIOD + 0.5), // RELEASE_COUNT
		int32_t((1.0 - WAVETABLE_DECIBEL_SHIFT(-91.6)) * AudioSynthWavetable::UNITY_GAIN), // SUSTAIN_MULT
		uint32_t(0.00 * AudioSynthWavetable::SAMPLES_PER_MSEC / (2 * AudioSynthWavetable::LFO_PERIOD)), // VIBRATO_DELAY
		uint32_t(0.1 * AudioSynthWavetable::LFO_PERIOD * (UINT32_MAX / AUDIO_SAMPLE_RATE_EXACT)), // VIBRATO_INCREMENT
		(WAVETABLE_CENTS_SHIFT(0) - 1.0) * 4, // VIBRATO_PITCH_COEFFICIENT_INITIAL
		(1.0 - WAVETABLE_CENTS_SHIFT(0)) * 4, // VIBRATO_COEFFICIENT_SECONDARY
		uint32_t(0.00 * AudioSynthWavetable::SAMPLES_PER_MSEC / (2 * AudioSynthWavetable::LFO_PERIOD)), // MODULATION_DELAY
		uint32_t(5.4 * AudioSynthWavetable::LFO_PERIOD * (UINT32_MAX / AUDIO_SAMPLE_RATE_EXACT)), // MODULATION_INCREMENT
		(WAVETABLE_CENTS_SHIFT(0) - 1.0) * 4, // MODULATION_PITCH_COEFFICIENT_INITIAL
		(1.0 - WAVETABLE_CENTS_SHIFT(0)) * 4, // MODULATION_PITCH_COEFFICIENT_SECOND
		int32_t(UINT16_MAX * (WAVETABLE_DECIBEL_SHIFT(0) - 1.0)) * 4, // MODULATION_AMPLITUDE_INITIAL_GAIN
		int32_t(UINT16_MAX * (1.0 - WAVETABLE_DECIBEL_SHIFT(0))) * 4, // MODULATION_AMPLITUDE_FINAL_GAIN
	},
	{
		(int16_t*)sample_3_distortiongt_distgtrd4, // sample
		true, // LOOP
		11, // LENGTH_BITS
		(1 << (32 - 11)) * WAVETABLE_CENTS_SHIFT(-4) * 44100.0 / WAVETABLE_NOTE_TO_FREQUENCY(91) / AUDIO_SAMPLE_RATE_EXACT + 0.5, // PER_HERTZ_PHASE_INCREMENT
		((uint32_t)1765 - 1) << (32 - 11), // MAX_PHASE
		((uint32_t)1761 - 1) << (32 - 11), // LOOP_PHASE_END
		(((uint32_t)1761 - 1) << (32 - 11)) - (((uint32_t)1593 - 1) << (32 - 11)), // LOOP_PHASE_LENGTH
		uint16_t(UINT16_MAX * WAVETABLE_DECIBEL_SHIFT(-7.5)), // INITIAL_ATTENUATION_SCALAR
		uint32_t(0.00 * AudioSynthWavetable::SAMPLES_PER_MSEC / AudioSynthWavetable::ENVELOPE_PERIOD + 0.5), // DELAY_COUNT
		uint32_t(6.20 * AudioSynthWavetable::SAMPLES_PER_MSEC / AudioSynthWavetable::ENVELOPE_PERIOD + 0.5), // ATTACK_COUNT
		uint32_t(20.01 * AudioSynthWavetable::SAMPLES_PER_MSEC / AudioSynthWavetable::ENVELOPE_PERIOD + 0.5), // HOLD_COUNT
		uint32_t(19596.17 * AudioSynthWavetable::SAMPLES_PER_MSEC / AudioSynthWavetable::ENVELOPE_PERIOD + 0.5), // DECAY_COUNT
		uint32_t(100.02 * AudioSynthWavetable::SAMPLES_PER_MSEC / AudioSynthWavetable::ENVELOPE_PERIOD + 0.5), // RELEASE_COUNT
		int32_t((1.0 - WAVETABLE_DECIBEL_SHIFT(-91.6)) * AudioSynthWavetable::UNITY_GAIN), // SUSTAIN_MULT
		uint32_t(0.00 * AudioSynthWavetable::SAMPLES_PER_MSEC / (2 * AudioSynthWavetable::LFO_PERIOD)), // VIBRATO_DELAY
		uint32_t(0.1 * AudioSynthWavetable::LFO_PERIOD * (UINT32_MAX / AUDIO_SAMPLE_RATE_EXACT)), // VIBRATO_INCREMENT
		(WAVETABLE_CENTS_SHIFT(0) - 1.0) * 4, // VIBRATO_PITCH_COEFFICIENT_INITIAL
		(1.0 - WAVETABLE_CENTS_SHIFT(0)) * 4, // VIBRATO_COEFFICIENT_SECONDARY
		uint32_t(0.00 * AudioSynthWavetable::SAMPLES_PER_MSEC / (2 * AudioSynthWavetable::LFO_PERIOD)), // MODULATION_DELAY
		uint32_t(5.4 * AudioSynthWavetable::LFO_PERIOD * (UINT32_MAX / AUDIO_SAMPLE_RATE_EXACT)), // MODULATION_INCREMENT
		(WAVETABLE_CENTS_SHIFT(0) - 1.0) * 4, // MODULATION_PITCH_COEFFICIENT_INITIAL
		(1.0 - WAVETABLE_CENTS_SHIFT(0)) * 4, // MODULATION_PITCH_COEFFICIENT_SECOND
		int32_t(UINT16_MAX * (WAVETABLE_DECIBEL_SHIFT(0) - 1.0)) * 4, // MODULATION_AMPLITUDE_INITIAL_GAIN
		int32_t(UINT16_MAX * (1.0 - WAVETABLE_DECIBEL_SHIFT(0))) * 4, // MODULATION_AMPLITUDE_FINAL_GAIN
	},
};

PROGMEM const uint32_t sample_0_distortiongt_distgtra2[1024] = {
0x00000000,0xfd58fbd7,0xfdc2fd4c,0xfd0ffdb3,0xfb83fc31,0xfbebfbb8,0xfbf2fc25,0xfcc3fc2a,
0xfec0fde5,0xffeaff73,0x00d30092,0x003700b7,0x00d10037,0x02f60209,0x02a50337,0x016501de,
0x01c30198,0x023401de,0x03ae0300,0x039203e0,0x024d0305,0x01f001d2,0x01890220,0xfeff0037,
0xfea2fe7f,0xffb5ff2a,0xffd3000c,0xfe8cff37,0xfe33fe36,0xfdcafe3b,0xfc39fcf6,0xfc3bfc13,
0xfbdcfc2f,0xfbd9fba4,0xfd88fc8f,0x0007febb,0x02570159,0x01a40291,0xfe0effdb,0xfcbefd00,
0xfc94fcc6,0xf9e6fbb8,0xf576f778,0xf5e7f4c8,0xfe36f924,0x04df0314,0x00880314,0x02310034,
0x070e04e6,0x09960888,0x0ab80a41,0x0a2a0ad3,0x07dd090b,0x061a06d9,0x05a805b5,0x03bd053f,
0xffb0017c,0xfe36fed5,0xfbd7fcfb,0xfdedfc13,0x0032ffc7,0xfea2ff67,0xfdf7fe61,0xfcdffd3f,
0xfe54fd56,0xff2dff2d,0xfc84fdfc,0xfe5efc82,0xfea5ffdb,0xf752fb1f,0xf43bf4f0,0xf365f445,
0xebdff071,0xe694e7b1,0xf6edeb4b,0x193007bf,0x2785254e,0x18132088,0x16711503,0x11281632,
0x05280a3c,0xfe1801d7,0xf727f9f0,0xf65bf659,0xf385f5a8,0xf087f0f1,0xf8e0f3e8,0xfaa3fb83,
0xf5c1f83c,0xedf8f252,0xecc2eb3c,0xf6f7f1e8,0xf910f947,0xf52af77a,0xf18bf2d7,0xf1c0f179,
0xf023f126,0xfedff2cd,0x2fdd1628,0x32443b67,0x19b021ac,0x1e001ba8,0x15cd1afd,0x110412b1,
0x08030e01,0xf3fefedc,0xe3daea59,0xda8ddf53,0xd362d5b5,0xda67d534,0xe9d1e1b4,0xf234f028,
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
0xf2affc24,0x0dcef00c,0x59b5466d,0x0ea62d35,0x1f941a8a,0xc9c40453,0xc74ea3d7,0xebeff4e5,
0xf75be307,0xf96b00c5,0x1ec5fade,0x6a5c5e45,0xe8f72ca3,0xcd40ca0a,0xec93e3c4,0x0a85e89e,
0x51fa490c,0x0a311eab,0x1e591c0c,0xc24dfe93,0xcb50a3ac,0xe74af276,0xf2f3e135,0xf06df897,
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
};
