prajwal1121/Portable-Synth/Version 1/Code/Sequencer+Recording/1_SequenceAndRecord/piano_samples.cpp

#include "piano_samples.h"
const AudioSynthWavetable::sample_data piano_samples[4] = {
	{
		(int16_t*)sample_0_piano_kpianob1, // sample
		true, // LOOP
		15, // LENGTH_BITS
		(1 << (32 - 15)) * WAVETABLE_CENTS_SHIFT(-43) * 44100.0 / WAVETABLE_NOTE_TO_FREQUENCY(75) / AUDIO_SAMPLE_RATE_EXACT + 0.5, // PER_HERTZ_PHASE_INCREMENT
		((uint32_t)17231 - 1) << (32 - 15), // MAX_PHASE
		((uint32_t)17227 - 1) << (32 - 15), // LOOP_PHASE_END
		(((uint32_t)17227 - 1) << (32 - 15)) - (((uint32_t)10655 - 1) << (32 - 15)), // LOOP_PHASE_LENGTH
		uint16_t(UINT16_MAX * WAVETABLE_DECIBEL_SHIFT(-15.0)), // INITIAL_ATTENUATION_SCALAR
		uint32_t(0.00 * AudioSynthWavetable::SAMPLES_PER_MSEC / AudioSynthWavetable::ENVELOPE_PERIOD + 0.5), // DELAY_COUNT
		uint32_t(6.20 * AudioSynthWavetable::SAMPLES_PER_MSEC / AudioSynthWavetable::ENVELOPE_PERIOD + 0.5), // ATTACK_COUNT
		uint32_t(630.32 * AudioSynthWavetable::SAMPLES_PER_MSEC / AudioSynthWavetable::ENVELOPE_PERIOD + 0.5), // HOLD_COUNT
		uint32_t(12596.93 * AudioSynthWavetable::SAMPLES_PER_MSEC / AudioSynthWavetable::ENVELOPE_PERIOD + 0.5), // DECAY_COUNT
		uint32_t(918.06 * AudioSynthWavetable::SAMPLES_PER_MSEC / AudioSynthWavetable::ENVELOPE_PERIOD + 0.5), // RELEASE_COUNT
		int32_t((1.0 - WAVETABLE_DECIBEL_SHIFT(-100.0)) * AudioSynthWavetable::UNITY_GAIN), // SUSTAIN_MULT
		uint32_t(0.00 * AudioSynthWavetable::SAMPLES_PER_MSEC / (2 * AudioSynthWavetable::LFO_PERIOD)), // VIBRATO_DELAY
		uint32_t(0.1 * AudioSynthWavetable::LFO_PERIOD * (UINT32_MAX / AUDIO_SAMPLE_RATE_EXACT)), // VIBRATO_INCREMENT
		(WAVETABLE_CENTS_SHIFT(0) - 1.0) * 4, // VIBRATO_PITCH_COEFFICIENT_INITIAL
		(1.0 - WAVETABLE_CENTS_SHIFT(0)) * 4, // VIBRATO_COEFFICIENT_SECONDARY
		uint32_t(0.00 * AudioSynthWavetable::SAMPLES_PER_MSEC / (2 * AudioSynthWavetable::LFO_PERIOD)), // MODULATION_DELAY
		uint32_t(5.4 * AudioSynthWavetable::LFO_PERIOD * (UINT32_MAX / AUDIO_SAMPLE_RATE_EXACT)), // MODULATION_INCREMENT
		(WAVETABLE_CENTS_SHIFT(0) - 1.0) * 4, // MODULATION_PITCH_COEFFICIENT_INITIAL
		(1.0 - WAVETABLE_CENTS_SHIFT(0)) * 4, // MODULATION_PITCH_COEFFICIENT_SECOND
		int32_t(UINT16_MAX * (WAVETABLE_DECIBEL_SHIFT(0) - 1.0)) * 4, // MODULATION_AMPLITUDE_INITIAL_GAIN
		int32_t(UINT16_MAX * (1.0 - WAVETABLE_DECIBEL_SHIFT(0))) * 4, // MODULATION_AMPLITUDE_FINAL_GAIN
	},
	{
		(int16_t*)sample_1_piano_kpianocx4, // sample
		true, // LOOP
		15, // LENGTH_BITS
		(1 << (32 - 15)) * WAVETABLE_CENTS_SHIFT(4) * 44100.0 / WAVETABLE_NOTE_TO_FREQUENCY(77) / AUDIO_SAMPLE_RATE_EXACT + 0.5, // PER_HERTZ_PHASE_INCREMENT
		((uint32_t)21573 - 1) << (32 - 15), // MAX_PHASE
		((uint32_t)21569 - 1) << (32 - 15), // LOOP_PHASE_END
		(((uint32_t)21569 - 1) << (32 - 15)) - (((uint32_t)21506 - 1) << (32 - 15)), // LOOP_PHASE_LENGTH
		uint16_t(UINT16_MAX * WAVETABLE_DECIBEL_SHIFT(-15.0)), // INITIAL_ATTENUATION_SCALAR
		uint32_t(0.00 * AudioSynthWavetable::SAMPLES_PER_MSEC / AudioSynthWavetable::ENVELOPE_PERIOD + 0.5), // DELAY_COUNT
		uint32_t(6.20 * AudioSynthWavetable::SAMPLES_PER_MSEC / AudioSynthWavetable::ENVELOPE_PERIOD + 0.5), // ATTACK_COUNT
		uint32_t(630.32 * AudioSynthWavetable::SAMPLES_PER_MSEC / AudioSynthWavetable::ENVELOPE_PERIOD + 0.5), // HOLD_COUNT
		uint32_t(12596.93 * AudioSynthWavetable::SAMPLES_PER_MSEC / AudioSynthWavetable::ENVELOPE_PERIOD + 0.5), // DECAY_COUNT
		uint32_t(918.06 * AudioSynthWavetable::SAMPLES_PER_MSEC / AudioSynthWavetable::ENVELOPE_PERIOD + 0.5), // RELEASE_COUNT
		int32_t((1.0 - WAVETABLE_DECIBEL_SHIFT(-100.0)) * AudioSynthWavetable::UNITY_GAIN), // SUSTAIN_MULT
		uint32_t(0.00 * AudioSynthWavetable::SAMPLES_PER_MSEC / (2 * AudioSynthWavetable::LFO_PERIOD)), // VIBRATO_DELAY
		uint32_t(0.1 * AudioSynthWavetable::LFO_PERIOD * (UINT32_MAX / AUDIO_SAMPLE_RATE_EXACT)), // VIBRATO_INCREMENT
		(WAVETABLE_CENTS_SHIFT(0) - 1.0) * 4, // VIBRATO_PITCH_COEFFICIENT_INITIAL
		(1.0 - WAVETABLE_CENTS_SHIFT(0)) * 4, // VIBRATO_COEFFICIENT_SECONDARY
		uint32_t(0.00 * AudioSynthWavetable::SAMPLES_PER_MSEC / (2 * AudioSynthWavetable::LFO_PERIOD)), // MODULATION_DELAY
		uint32_t(5.4 * AudioSynthWavetable::LFO_PERIOD * (UINT32_MAX / AUDIO_SAMPLE_RATE_EXACT)), // MODULATION_INCREMENT
		(WAVETABLE_CENTS_SHIFT(0) - 1.0) * 4, // MODULATION_PITCH_COEFFICIENT_INITIAL
		(1.0 - WAVETABLE_CENTS_SHIFT(0)) * 4, // MODULATION_PITCH_COEFFICIENT_SECOND
		int32_t(UINT16_MAX * (WAVETABLE_DECIBEL_SHIFT(0) - 1.0)) * 4, // MODULATION_AMPLITUDE_INITIAL_GAIN
		int32_t(UINT16_MAX * (1.0 - WAVETABLE_DECIBEL_SHIFT(0))) * 4, // MODULATION_AMPLITUDE_FINAL_GAIN
	},
	{
		(int16_t*)sample_2_piano_kpianodx5, // sample
		true, // LOOP
		13, // LENGTH_BITS
		(1 << (32 - 13)) * WAVETABLE_CENTS_SHIFT(29) * 44100.0 / WAVETABLE_NOTE_TO_FREQUENCY(106) / AUDIO_SAMPLE_RATE_EXACT + 0.5, // PER_HERTZ_PHASE_INCREMENT
		((uint32_t)6145 - 1) << (32 - 13), // MAX_PHASE
		((uint32_t)6141 - 1) << (32 - 13), // LOOP_PHASE_END
		(((uint32_t)6141 - 1) << (32 - 13)) - (((uint32_t)6093 - 1) << (32 - 13)), // LOOP_PHASE_LENGTH
		uint16_t(UINT16_MAX * WAVETABLE_DECIBEL_SHIFT(-15.0)), // INITIAL_ATTENUATION_SCALAR
		uint32_t(0.00 * AudioSynthWavetable::SAMPLES_PER_MSEC / AudioSynthWavetable::ENVELOPE_PERIOD + 0.5), // DELAY_COUNT
		uint32_t(6.20 * AudioSynthWavetable::SAMPLES_PER_MSEC / AudioSynthWavetable::ENVELOPE_PERIOD + 0.5), // ATTACK_COUNT
		uint32_t(630.32 * AudioSynthWavetable::SAMPLES_PER_MSEC / AudioSynthWavetable::ENVELOPE_PERIOD + 0.5), // HOLD_COUNT
		uint32_t(12596.93 * AudioSynthWavetable::SAMPLES_PER_MSEC / AudioSynthWavetable::ENVELOPE_PERIOD + 0.5), // DECAY_COUNT
		uint32_t(918.06 * AudioSynthWavetable::SAMPLES_PER_MSEC / AudioSynthWavetable::ENVELOPE_PERIOD + 0.5), // RELEASE_COUNT
		int32_t((1.0 - WAVETABLE_DECIBEL_SHIFT(-100.0)) * AudioSynthWavetable::UNITY_GAIN), // SUSTAIN_MULT
		uint32_t(0.00 * AudioSynthWavetable::SAMPLES_PER_MSEC / (2 * AudioSynthWavetable::LFO_PERIOD)), // VIBRATO_DELAY
		uint32_t(0.1 * AudioSynthWavetable::LFO_PERIOD * (UINT32_MAX / AUDIO_SAMPLE_RATE_EXACT)), // VIBRATO_INCREMENT
		(WAVETABLE_CENTS_SHIFT(0) - 1.0) * 4, // VIBRATO_PITCH_COEFFICIENT_INITIAL
		(1.0 - WAVETABLE_CENTS_SHIFT(0)) * 4, // VIBRATO_COEFFICIENT_SECONDARY
		uint32_t(0.00 * AudioSynthWavetable::SAMPLES_PER_MSEC / (2 * AudioSynthWavetable::LFO_PERIOD)), // MODULATION_DELAY
		uint32_t(5.4 * AudioSynthWavetable::LFO_PERIOD * (UINT32_MAX / AUDIO_SAMPLE_RATE_EXACT)), // MODULATION_INCREMENT
		(WAVETABLE_CENTS_SHIFT(0) - 1.0) * 4, // MODULATION_PITCH_COEFFICIENT_INITIAL
		(1.0 - WAVETABLE_CENTS_SHIFT(0)) * 4, // MODULATION_PITCH_COEFFICIENT_SECOND
		int32_t(UINT16_MAX * (WAVETABLE_DECIBEL_SHIFT(0) - 1.0)) * 4, // MODULATION_AMPLITUDE_INITIAL_GAIN
		int32_t(UINT16_MAX * (1.0 - WAVETABLE_DECIBEL_SHIFT(0))) * 4, // MODULATION_AMPLITUDE_FINAL_GAIN
	},
	{
		(int16_t*)sample_3_piano_kpianof502, // sample
		true, // LOOP
		13, // LENGTH_BITS
		(1 << (32 - 13)) * WAVETABLE_CENTS_SHIFT(30) * 44100.0 / WAVETABLE_NOTE_TO_FREQUENCY(111) / AUDIO_SAMPLE_RATE_EXACT + 0.5, // PER_HERTZ_PHASE_INCREMENT
		((uint32_t)4463 - 1) << (32 - 13), // MAX_PHASE
		((uint32_t)4202 - 1) << (32 - 13), // LOOP_PHASE_END
		(((uint32_t)4202 - 1) << (32 - 13)) - (((uint32_t)4148 - 1) << (32 - 13)), // LOOP_PHASE_LENGTH
		uint16_t(UINT16_MAX * WAVETABLE_DECIBEL_SHIFT(-15.0)), // INITIAL_ATTENUATION_SCALAR
		uint32_t(0.00 * AudioSynthWavetable::SAMPLES_PER_MSEC / AudioSynthWavetable::ENVELOPE_PERIOD + 0.5), // DELAY_COUNT
		uint32_t(6.20 * AudioSynthWavetable::SAMPLES_PER_MSEC / AudioSynthWavetable::ENVELOPE_PERIOD + 0.5), // ATTACK_COUNT
		uint32_t(630.32 * AudioSynthWavetable::SAMPLES_PER_MSEC / AudioSynthWavetable::ENVELOPE_PERIOD + 0.5), // HOLD_COUNT
		uint32_t(12596.93 * AudioSynthWavetable::SAMPLES_PER_MSEC / AudioSynthWavetable::ENVELOPE_PERIOD + 0.5), // DECAY_COUNT
		uint32_t(918.06 * AudioSynthWavetable::SAMPLES_PER_MSEC / AudioSynthWavetable::ENVELOPE_PERIOD + 0.5), // RELEASE_COUNT
		int32_t((1.0 - WAVETABLE_DECIBEL_SHIFT(-100.0)) * AudioSynthWavetable::UNITY_GAIN), // SUSTAIN_MULT
		uint32_t(0.00 * AudioSynthWavetable::SAMPLES_PER_MSEC / (2 * AudioSynthWavetable::LFO_PERIOD)), // VIBRATO_DELAY
		uint32_t(0.1 * AudioSynthWavetable::LFO_PERIOD * (UINT32_MAX / AUDIO_SAMPLE_RATE_EXACT)), // VIBRATO_INCREMENT
		(WAVETABLE_CENTS_SHIFT(0) - 1.0) * 4, // VIBRATO_PITCH_COEFFICIENT_INITIAL
		(1.0 - WAVETABLE_CENTS_SHIFT(0)) * 4, // VIBRATO_COEFFICIENT_SECONDARY
		uint32_t(0.00 * AudioSynthWavetable::SAMPLES_PER_MSEC / (2 * AudioSynthWavetable::LFO_PERIOD)), // MODULATION_DELAY
		uint32_t(5.4 * AudioSynthWavetable::LFO_PERIOD * (UINT32_MAX / AUDIO_SAMPLE_RATE_EXACT)), // MODULATION_INCREMENT
		(WAVETABLE_CENTS_SHIFT(0) - 1.0) * 4, // MODULATION_PITCH_COEFFICIENT_INITIAL
		(1.0 - WAVETABLE_CENTS_SHIFT(0)) * 4, // MODULATION_PITCH_COEFFICIENT_SECOND
		int32_t(UINT16_MAX * (WAVETABLE_DECIBEL_SHIFT(0) - 1.0)) * 4, // MODULATION_AMPLITUDE_INITIAL_GAIN
		int32_t(UINT16_MAX * (1.0 - WAVETABLE_DECIBEL_SHIFT(0))) * 4, // MODULATION_AMPLITUDE_FINAL_GAIN
	},
};

PROGMEM const uint32_t sample_0_piano_kpianob1[8704] = {
0x00000000,0xff2cfe83,0x006fffd0,0x01b0008d,0x03ec01fd,0x060e06f1,0x080b057c,0x036a0618,
0x03fe02b7,0xffe30299,0x031601e9,0x02ca0252,0x02aefe06,0xf4fffa2f,0xfafcfdd6,0xfa0eff91,
0xfb320136,0xf2d9f597,0x0176f6be,0xfdaafbeb,0x1045fa37,0xfd460886,0xff85f155,0xdb9aef93,
0xecb1cec4,0x0dbd19bf,0xe8a3f8f1,0xf1b7dd57,0xf864f4cd,0xd777fd52,0xe036ebc9,0x0384eabf,
0x13eb306a,0x229bee8e,0x396e334b,0x5cfc4406,0x49ea59e2,0x296c36aa,0x2b983360,0x152e23bb,
0xf7a30a12,0xecb4fc65,0x07c9d148,0xf0a62714,0xcf67d21f,0xb82ebaf3,0xfcacedb3,0xfeeafa87,
0xbed6bead,0xf0eac99d,0x144c1237,0xfaf3fa51,0x078e1546,0x036a0839,0x094b033b,0xe53ae6ea,
0xe381d18b,0xc6bbf99d,0xab11ba19,0xcd13b70b,0xc968ceb1,0xe234e14d,0x075ef93d,0xece20f9c,
0xf8dee7f7,0x2eb9f537,0x52db5f66,0x414a47ce,0x1f6831e1,0x3ed52d0e,0x46573b4e,0x4ae5499e,
0x12e33fe9,0x27eb012f,0x25f4259b,0x063b28ac,0xff00d963,0x1d0f1b73,0xffbe2021,0xb803d098,
0xbb6cb475,0x0163ffd2,0xe385f65d,0xcf6ac5b2,0xf35bef5b,0xfe51e7e0,0xffa100ab,0xec71e6d8,
0xffa0f469,0xfa700ecd,0x197ffde6,0x187f21b4,0xcec1f1c0,0xcdc2cebc,0xbd13bc82,0xbf79c234,
0xe863cacd,0xfbcbf8b3,0xd4a4fd62,0xeb23ccc2,0x36741823,0x54ad3df9,0x34734827,0x25ff2794,
0x361438bf,0x4f823743,0x288f59c5,0x31a32e4c,0x2b322100,0x04013121,0xe82adf1a,0x211af9a5,
0x04163146,0xc45cf515,0x92b39737,0xd375b70c,0xf060e986,0xda5ebc38,0xf784e4c7,0xf5ebeef8,
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
0x46e64a3b,0x14cd245d,0xb3abcab4,0xdccec01c,0x4f581265,0x2d3444ee,0xcc521874,0xc081ba7b,
0x13aaddf4,0x3fcc51b6,0x168a33e0,0xbcc3cd43,0xd7f0bef5,0x4a23114d,0x326e33db,0xcb0d0b99,
0xbed3ba8d,0x14efd458,0x3211477c,0x045835b1,0xb9f4cc6e,0xd6ffc25c,0x48221fc7,0x3a7f35ba,
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
};
